EtEsWieEtEs/myT40-PLC/myT40-Controller/Prototype_V1/V1_CONTR_BOT.jpg

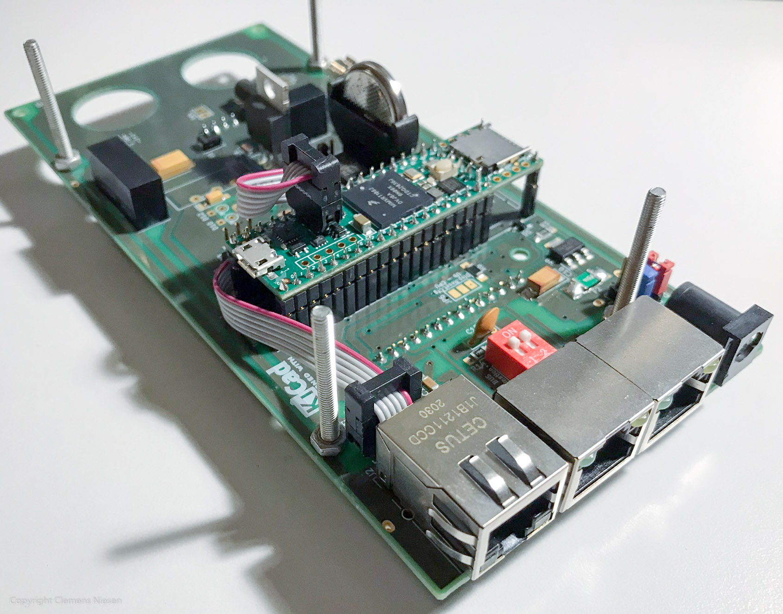
myT40-Controller/Prototype_V1/V1_CONTR_BOT.jpg
