EtEsWieEtEs/myT40-PLC/myT40-Controller/Prototype_V3_Final/myT40-C-V3.1-M10_BOT.png

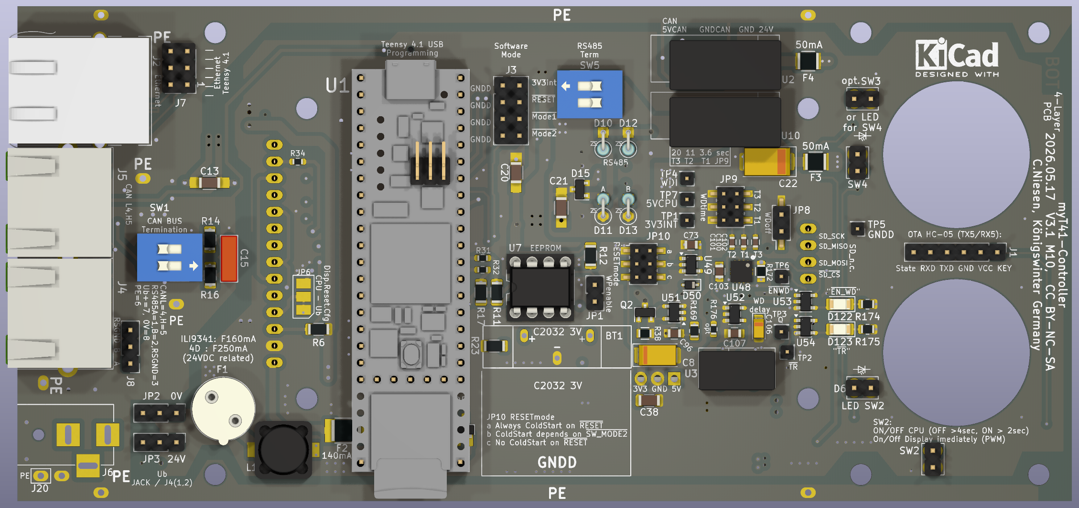
myT40-Controller/Prototype_V3_Final/myT40-C-V3.1-M10_BOT.png
