EtEsWieEtEs/myT40-PLC/myT40-Controller/Prototype_V3_Final/myT40-C-V3.1-M10_TOP.png

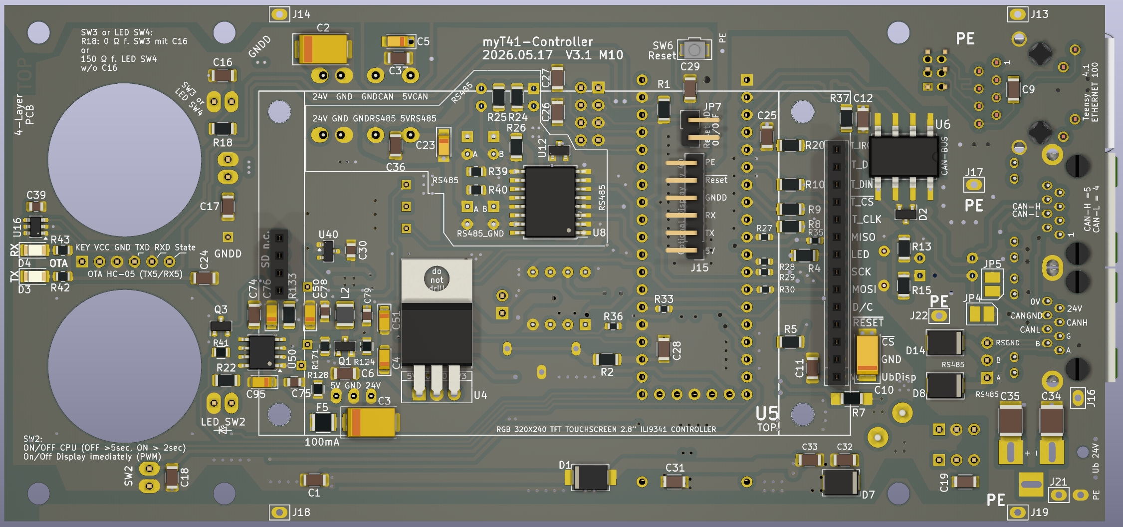
myT40-Controller/Prototype_V3_Final/myT40-C-V3.1-M10_TOP.png
