EtEsWieEtEs/myT40-PLC/myT40-EXT-116-XD1/Pictures/IMG_20240401_113943.jpg

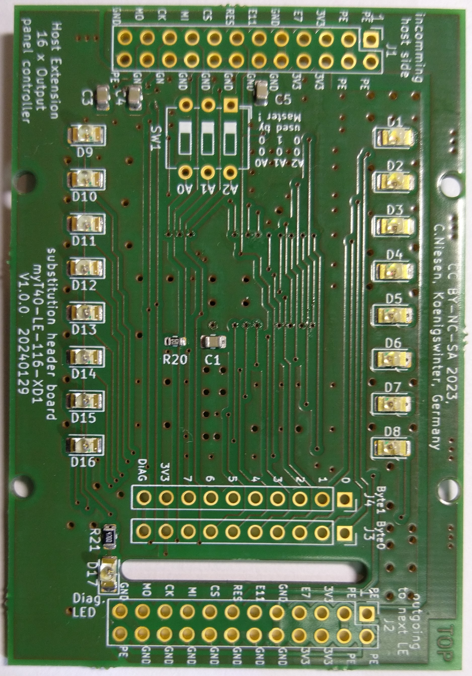
myT40-EXT-116-XD1/Pictures/IMG_20240401_113943.jpg
