EtEsWieEtEs/myT40-PLC/myT40-EXT-116-XD1/Pictures/IMG_20240401_123307.jpg

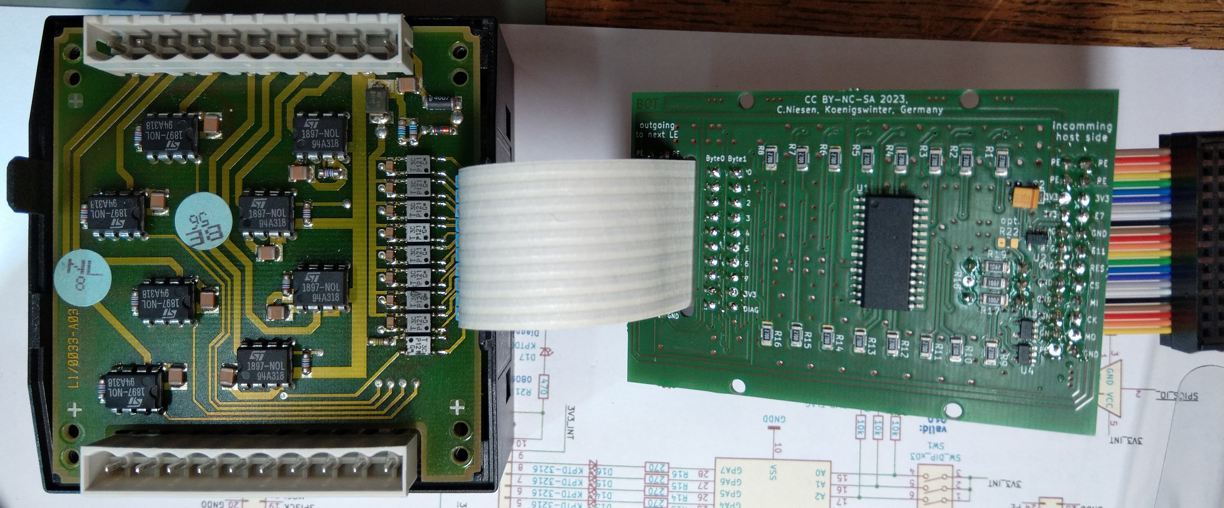
myT40-EXT-116-XD1/Pictures/IMG_20240401_123307.jpg
