EtEsWieEtEs/myT40-PLC/myT40-PLC/Prototype_V5_Final/myT40-PLC-V5_UP-TOP.png

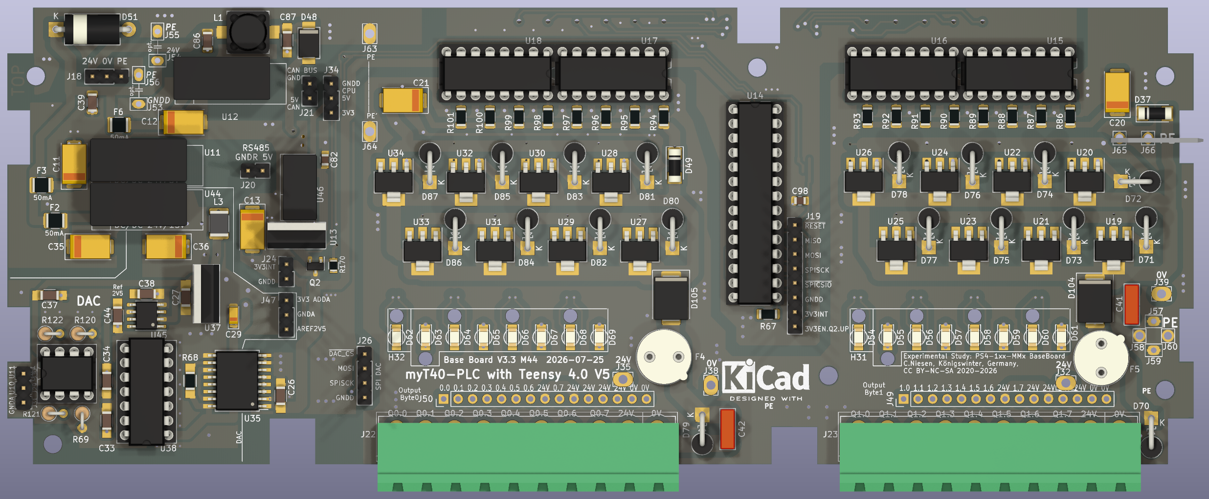
myT40-PLC/Prototype_V5_Final/myT40-PLC-V5_UP-TOP.png
